NikodemBartnik/ReactionWheel/CAD/old1/pin.stl

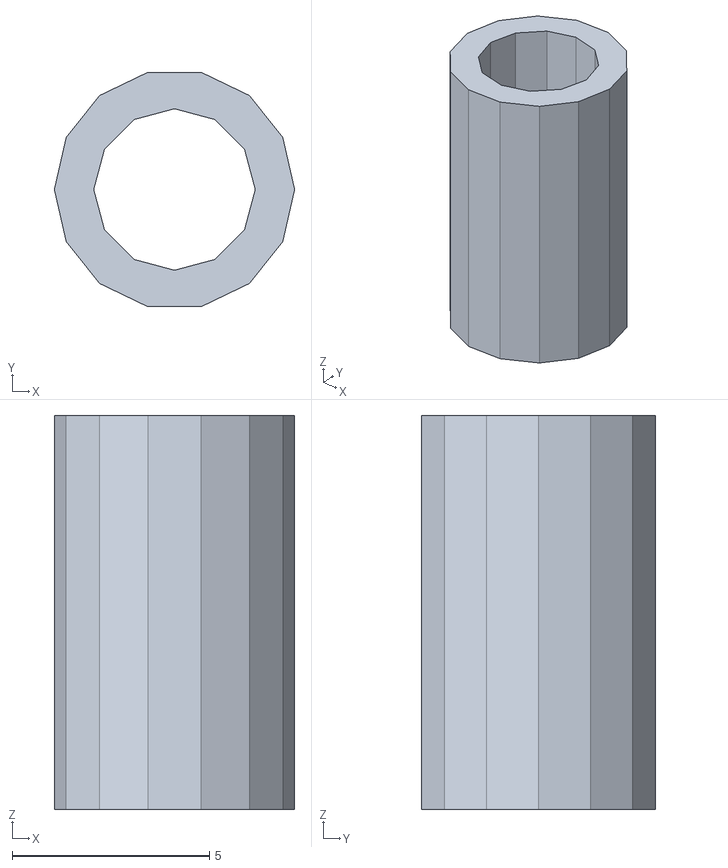
[picture p16: CAD file, 2024-03-29, an earlier design]
CAD/old1/pin.stl
6.10 x 5.95 x 10.0
