NikodemBartnik/ReactionWheel/CAD/old1/base (1).stl

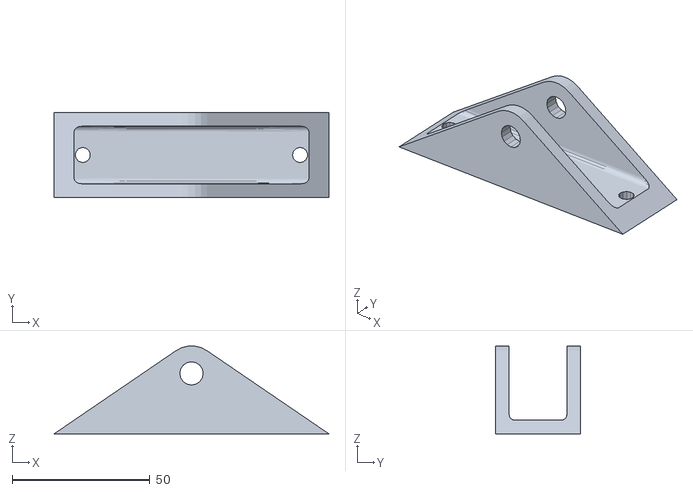
[picture p17: CAD file, 2024-03-29, an earlier design]
CAD/old1/base (1).stl
100.0 x 31.0 x 31.9
