NikodemBartnik/ReactionWheel/CAD/old1/base (2).stl

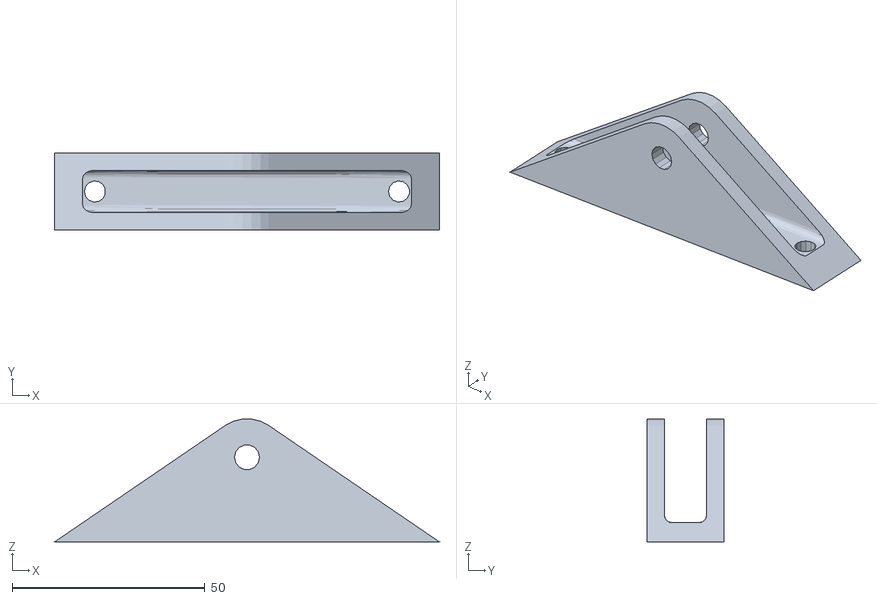
[picture p18: CAD file, 2024-03-29, an earlier design]
CAD/old1/base (2).stl
100.0 x 20.0 x 31.9
